Hal9k-dk/bigbro/esp32/main/bigbro.cpp

#include <stdio.h>

#include <esp_app_desc.h>
#include <esp_event.h>
#include <esp_log.h>
#include <esp_wifi.h>
#include <freertos/FreeRTOS.h>
#include <freertos/task.h>
#include <nvs_flash.h>

#include "cardcache.h"
#include "connect.h"
#include "console.h"
#include "controller.h"
#include "defs.h"
#include "display.h"
#include "format.h"
#include "hw.h"
#include "mqtt.h"
#include "nvs.h"
#include "otafwu.h"
#include "reader.h"
#include "sntp.h"

static constexpr const char* TAG = "bigbro";

extern "C"
void app_main()
{
    init_hardware();

    const auto app_desc = esp_app_get_description();
    printf("BigBro v %s\n", app_desc->version);

    mount_spiffs("/spiffs", "font", 10);
    
    TFT_t tft;
    Display display(&tft);
    set_backlight(255);
    
    display.add_progress(format("BigBro v %s", app_desc->version));

    display.add_progress("NVS init");

    init_nvs();

    display.add_progress(get_identifier());

    bool connected = false;
    const auto wifi_creds = get_wifi_creds();
    if (!wifi_creds.empty())
    {
        ESP_ERROR_CHECK(esp_netif_init());
        ESP_ERROR_CHECK(esp_event_loop_create_default());

        display.add_progress("Connect to WiFi");

        int attempts_left = 5;
        while (!connected && attempts_left)
        {
            connected = connect(wifi_creds);
            ESP_LOGI(TAG, "Connected: %d attempts: %d",
                     connected, attempts_left);
            if (!connected)
            {
                disconnect();
                vTaskDelay(10000 / portTICK_PERIOD_MS);
                --attempts_left;
            }
        }
        if (connected)
        {
            ESP_LOGI(TAG, "Connected to WiFi");
            ESP_ERROR_CHECK(esp_wifi_set_ps(WIFI_PS_NONE));

            display.add_progress("SNTP synch");

            initialize_sntp();
            
            Card_cache::instance().set_api_token(get_acs_token());
        }
    }
    
    xTaskCreate(rfid_task, "rfid_task", 4*1024, NULL, 5, NULL);

    printf("\n\nPress a key to enter console\n");
    bool debug = false;
    int keypresses = 0;
    for (int i = 0; i < 20; ++i)
    {
        const int c = getchar();
        if (c != EOF)
        {
            printf("Key: %d\n", c);
            ++keypresses;
            if (keypresses > 3)
            {
                debug = true;
                break;
            }
        }
        vTaskDelay(100/portTICK_PERIOD_MS);
    }

    bool ext1_state = gpio_get_level(PIN_EXT_1);
    bool switch_state = read_switch();
    if (!ext1_state || switch_state)
    {
        display.add_progress("OTA disabled");
        if (!ext1_state)
            printf("OTA firmware update disabled by EXT1\n");
        if (switch_state)
            printf("OTA firmware update disabled by card\n");
    }
    else if (!debug)
    {
        display.add_progress("OTA check");
        if (!check_ota_update(display))
            display.add_progress("FAILED!");
    }
    if (connected)
    {
        xTaskCreate(card_cache_task, "cache_task", 4*1024, NULL, 1, NULL);
        Mqtt::instance().start(get_mqtt_address());
    }
    xTaskCreate(cursense_task, "cursense_task", 2*1024, NULL, 1, NULL);

    if (debug)
        run_console(display);        // never returns

    Mqtt::instance().write_slack(format(":panopticon: BigBro %s", app_desc->version));
    
    esp_log_level_set("esp_wifi", ESP_LOG_ERROR);
    esp_log_level_set("wifi", ESP_LOG_ERROR);

    display.add_progress("Starting");
    Mqtt::instance().log(format("ACS frontend %s (%s)",
                                app_desc->version,
                                get_identifier().c_str()));

    Controller controller(display);
    display.clear();
    controller.run(); // never returns
}

// Local Variables:
// compile-command: "(cd ..; idf.py build)"
// End:
