Hal9k-dk/bigbro/esp32/main/otafwu.cpp

#include "display.h"
#include "http.h"

#include "freertos/FreeRTOS.h"
#include "freertos/task.h"
#include "esp_system.h"
#include "esp_event.h"
#include "esp_log.h"
#include "esp_ota_ops.h"
#include "esp_app_format.h"
#include "esp_http_client.h"
#include "esp_flash_partitions.h"
#include "esp_partition.h"
#include "nvs.h"
#include "nvs_flash.h"
#include "errno.h"

static constexpr const char* TAG = "ota";

static const constexpr int HASH_LEN = 32; // SHA-256 digest length
static const constexpr int BUFFSIZE = 1024;

bool check_ota_update(class Display& display)
{
    // Get SHA256 digest for the partition table
    esp_partition_t partition;
    partition.address   = ESP_PARTITION_TABLE_OFFSET;
    partition.size      = ESP_PARTITION_TABLE_MAX_LEN;
    partition.type      = ESP_PARTITION_TYPE_DATA;
    uint8_t sha_256[HASH_LEN] = { 0 };
    esp_partition_get_sha256(&partition, sha_256);

    // Get SHA256 digest for bootloader
    partition.address   = ESP_BOOTLOADER_OFFSET;
    partition.size      = ESP_PARTITION_TABLE_OFFSET;
    partition.type      = ESP_PARTITION_TYPE_APP;
    esp_partition_get_sha256(&partition, sha_256);

    // Get SHA256 digest for running partition
    esp_partition_get_sha256(esp_ota_get_running_partition(), sha_256);

    const esp_partition_t* running = esp_ota_get_running_partition();
    esp_ota_img_states_t ota_state;
    if (esp_ota_get_state_partition(running, &ota_state) == ESP_OK)
        if (ota_state == ESP_OTA_IMG_PENDING_VERIFY)
        {
            bool diagnostic_is_ok = true;
#if 0
            // later...
            diagnostic_is_ok = diagnostic();
#endif
            if (diagnostic_is_ok)
            {
                ESP_LOGI(TAG, "Diagnostics completed successfully! Continuing execution ...");
                esp_ota_mark_app_valid_cancel_rollback();
            }
            else
            {
                ESP_LOGE(TAG, "Diagnostics failed! Start rollback to the previous version ...");
                esp_ota_mark_app_invalid_rollback_and_reboot();
            }
        }

    const esp_partition_t* configured = esp_ota_get_boot_partition();
    running = esp_ota_get_running_partition();

    if (configured != running)
    {
        ESP_LOGW(TAG, "Configured OTA boot partition at offset 0x%08" PRIx32 ", but running from offset 0x%08" PRIx32,
                 configured->address, running->address);
        ESP_LOGW(TAG, "(This can happen if either the OTA boot data or preferred boot image become corrupted somehow.)");
    }
    ESP_LOGI(TAG, "Running partition type %d subtype %d (offset 0x%08" PRIx32 ")",
             running->type, running->subtype, running->address);

    esp_http_client_config_t config = {
        .host = "acsgateway.hal9k.dk",
        .path = "/firmware/bigbro2",
        .timeout_ms = 3000,
        .event_handler = http_event_handler,
        .transport_type = HTTP_TRANSPORT_OVER_SSL,
        .crt_bundle_attach = esp_crt_bundle_attach,
        .keep_alive_enable = true,
    };

    esp_http_client_handle_t client = esp_http_client_init(&config);
    if (!client)
    {
        ESP_LOGE(TAG, "Failed to initialise HTTP connection");
        return false;
    }
    Http_client_wrapper w(client);
    esp_err_t err = esp_http_client_open(client, 0);
    if (err != ESP_OK)
    {
        ESP_LOGE(TAG, "Failed to open HTTP connection: %s", esp_err_to_name(err));
        return false;
    }
    esp_http_client_fetch_headers(client);
    const int status_code = esp_http_client_get_status_code(client);
    if (status_code != 200)
    {
        ESP_LOGE(TAG, "OTA HTTP error: %d", status_code);
        return false;
    }

    const esp_partition_t* update_partition = esp_ota_get_next_update_partition(NULL);
    assert(update_partition != NULL);
    ESP_LOGI(TAG, "Writing to partition subtype %d at offset 0x%" PRIx32,
             update_partition->subtype, update_partition->address);

    int binary_file_length = 0;
    bool image_header_was_checked = false;
    // update handle : set by esp_ota_begin(), must be freed via esp_ota_end()
    esp_ota_handle_t update_handle = 0;
    while (1)
    {
        char ota_write_data[BUFFSIZE + 1] = { 0 };
        int data_read = esp_http_client_read(client, ota_write_data, BUFFSIZE);
        if (data_read < 0)
        {
            ESP_LOGE(TAG, "Error: SSL data read error");
            return false;
        }
        if (data_read > 0)
        {
            if (!image_header_was_checked)
            {
                if (data_read > sizeof(esp_image_header_t) + sizeof(esp_image_segment_header_t)
                    + sizeof(esp_app_desc_t))
                {
                    // check current version with downloading
                    esp_app_desc_t new_app_info;
                    memcpy(&new_app_info,
                           &ota_write_data[sizeof(esp_image_header_t)
                                           + sizeof(esp_image_segment_header_t)],
                           sizeof(esp_app_desc_t));
                    ESP_LOGI(TAG, "New firmware version: %s", new_app_info.version);

                    esp_app_desc_t running_app_info;
                    if (esp_ota_get_partition_description(running, &running_app_info) == ESP_OK)
                        ESP_LOGI(TAG, "Running firmware version: %s", running_app_info.version);

                    const esp_partition_t* last_invalid_app = esp_ota_get_last_invalid_partition();
                    esp_app_desc_t invalid_app_info;
                    if (esp_ota_get_partition_description(last_invalid_app, &invalid_app_info) == ESP_OK)
                        ESP_LOGI(TAG, "Last invalid firmware version: %s", invalid_app_info.version);

                    // check current version with last invalid partition
                    if (last_invalid_app)
                    {
                        if (memcmp(invalid_app_info.version, new_app_info.version, sizeof(new_app_info.version)) == 0)
                        {
                            ESP_LOGW(TAG, "New version is the same as invalid version.");
                            ESP_LOGW(TAG, "Previously, there was an attempt to launch the firmware with %s version, but it failed.",
                                     invalid_app_info.version);
                            ESP_LOGW(TAG, "The firmware has been rolled back to the previous version.");
                            display.add_progress("Rolled back");
                            return true;
                        }
                    }
                    if (memcmp(new_app_info.version, running_app_info.version, sizeof(new_app_info.version)) == 0)
                    {
                        if (gpio_get_level((gpio_num_t) 0))
                        {
                            ESP_LOGW(TAG, "Current running version is the same as a new. We will not continue the update.");
                            display.add_progress("No new version");
                            return true;
                        }
                        else
                        {
                            ESP_LOGI(TAG, "Forcing update");
                        }
                    }

                    image_header_was_checked = true;

                    err = esp_ota_begin(update_partition, OTA_WITH_SEQUENTIAL_WRITES, &update_handle);
                    if (err != ESP_OK)
                    {
                        ESP_LOGE(TAG, "esp_ota_begin failed (%s)", esp_err_to_name(err));
                        esp_ota_abort(update_handle);
                        return false;
                    }
                    ESP_LOGI(TAG, "esp_ota_begin succeeded");
                    display.add_progress("Downloading");
                }
                else
                {
                    ESP_LOGE(TAG, "received package is not fit len");
                    esp_ota_abort(update_handle);
                    return false;
                }
            }
            err = esp_ota_write(update_handle, (const void*) ota_write_data, data_read);
            if (err != ESP_OK)
            {
                esp_ota_abort(update_handle);
                return false;
            }
            binary_file_length += data_read;
            ESP_LOGD(TAG, "Written image length %d", binary_file_length);
        }
        else if (data_read == 0)
        {
            // As esp_http_client_read never returns negative error code, we rely on
            // `errno` to check for underlying transport connectivity closure if any
            if (errno == ECONNRESET || errno == ENOTCONN)
            {
                ESP_LOGE(TAG, "Connection closed, errno = %d", errno);
                break;
            }
            if (esp_http_client_is_complete_data_received(client))
            {
                ESP_LOGI(TAG, "Connection closed");
                break;
            }
        }
    }
    ESP_LOGI(TAG, "Total Write binary data length: %d", binary_file_length);
    if (!esp_http_client_is_complete_data_received(client))
    {
        ESP_LOGE(TAG, "Error in receiving complete file");
        esp_ota_abort(update_handle);
        return false;
    }

    err = esp_ota_end(update_handle);
    if (err != ESP_OK)
    {
        if (err == ESP_ERR_OTA_VALIDATE_FAILED)
            ESP_LOGE(TAG, "Image validation failed, image is corrupted");
        else 
            ESP_LOGE(TAG, "esp_ota_end failed (%s)!", esp_err_to_name(err));
        return false;
    }

    err = esp_ota_set_boot_partition(update_partition);
    if (err != ESP_OK)
    {
        ESP_LOGE(TAG, "esp_ota_set_boot_partition failed (%s)!", esp_err_to_name(err));
        return false;
    }
    display.add_progress("Rebooting");
    ESP_LOGI(TAG, "Prepare to restart system!");
    esp_restart();
    return true;
}

// Local Variables:
// compile-command: "(cd ..; idf.py build)"
// End:
