Hal9k-dk/bigbro/esp32/components/ili9340/ili9340.h

#ifndef MAIN_ILI9340_H_
#define MAIN_ILI9340_H_

#ifdef __cplusplus
extern "C" {
#endif

#include "driver/spi_master.h"
#include "fontx.h"

#define rgb565(r, g, b) (((r & 0xF8) << 8) | ((g & 0xFC) << 3) | (b >> 3))

#define RED    rgb565(255,   0,   0) // 0xf800
#define GREEN  rgb565(  0, 255,   0) // 0x07e0
#define BLUE   rgb565(  0,   0, 255) // 0x001f
#define BLACK  rgb565(  0,   0,   0) // 0x0000
#define WHITE  rgb565(255, 255, 255) // 0xffff
#define GRAY   rgb565(128, 128, 128) // 0x8410
#define YELLOW rgb565(255, 255,   0) // 0xFFE0
#define CYAN   rgb565(  0, 156, 209) // 0x04FA
#define PURPLE rgb565(128,   0, 128) // 0x8010

typedef enum {DIRECTION0, DIRECTION90, DIRECTION180, DIRECTION270} DIRECTION;

typedef struct {
	uint16_t _model;
	uint16_t _width;
	uint16_t _height;
	uint16_t _offsetx;
	uint16_t _offsety;
	uint16_t _font_direction;
	uint16_t _font_fill;
	uint16_t _font_fill_color;
	uint16_t _font_underline;
	uint16_t _font_underline_color;
	int16_t _dc;
	int16_t _bl;
	int16_t _irq;
	spi_device_handle_t _TFT_Handle;
	spi_device_handle_t _XPT_Handle;
	bool _calibration;
	int16_t _min_xp; // Minimum xp calibration
	int16_t _min_yp; // Minimum yp calibration
	int16_t _max_xp; // Maximum xp calibration
	int16_t _max_yp; // Maximum yp calibration
	int16_t _min_xc; // Minimum x coordinate
	int16_t _min_yc; // Minimum y coordinate
	int16_t _max_xc; // Maximum x coordinate
	int16_t _max_yc; // Maximum y coordinate
} TFT_t;

void spi_master_init(TFT_t * dev, int16_t TFT_MOSI, int16_t TFT_SCLK, int16_t TFT_CS, int16_t GPIO_DC, int16_t GPIO_RESET, int16_t GPIO_BL,
	int16_t XPT_MISO, int16_t XPT_CS, int16_t XPT_IRQ, int16_t XPT_SCLK, int16_t XPT_MOSI);
bool spi_master_write_byte(spi_device_handle_t SPIHandle, const uint8_t* Data, size_t DataLength);
bool spi_master_write_comm_byte(TFT_t * dev, uint8_t cmd);
bool spi_master_write_comm_word(TFT_t * dev, uint16_t cmd);
bool spi_master_write_data_byte(TFT_t * dev, uint8_t data);
bool spi_master_write_data_word(TFT_t * dev, uint16_t data);
bool spi_master_write_addr(TFT_t * dev, uint16_t addr1, uint16_t addr2);
bool spi_master_write_color(TFT_t * dev, uint16_t color, uint16_t size);
bool spi_master_write_colors(TFT_t * dev, uint16_t * colors, uint16_t size);

void delayMS(int ms);
void lcdWriteRegisterWord(TFT_t * dev, uint16_t addr, uint16_t data);
void lcdWriteRegisterByte(TFT_t * dev, uint8_t addr, uint16_t data);
void lcdInit(TFT_t * dev, uint16_t model, int width, int height, int offsetx, int offsety);
void lcdDrawPixel(TFT_t * dev, uint16_t x, uint16_t y, uint16_t color);
void lcdDrawMultiPixels(TFT_t * dev, uint16_t x, uint16_t y, uint16_t size, uint16_t * colors);
void lcdDrawFillRect(TFT_t * dev, uint16_t x1, uint16_t y1, uint16_t x2, uint16_t y2, uint16_t color);
void lcdDrawFillRect2(TFT_t * dev, uint16_t x0, uint16_t y0, uint16_t size, uint16_t color);
void lcdDisplayOff(TFT_t * dev);
void lcdDisplayOn(TFT_t * dev);
void lcdInversionOff(TFT_t * dev);
void lcdInversionOn(TFT_t * dev);
void lcdBGRFilter(TFT_t * dev);
void lcdFillScreen(TFT_t * dev, uint16_t color);
void lcdDrawLine(TFT_t * dev, uint16_t x1, uint16_t y1, uint16_t x2, uint16_t y2, uint16_t color);
void lcdDrawRect(TFT_t * dev, uint16_t x1, uint16_t y1, uint16_t x2, uint16_t y2, uint16_t color);
void lcdDrawRect2(TFT_t * dev, uint16_t x0, uint16_t y0, uint16_t size, uint16_t color);
void lcdDrawRectAngle(TFT_t * dev, uint16_t xc, uint16_t yc, uint16_t w, uint16_t h, uint16_t angle, uint16_t color);
void lcdDrawTriangle(TFT_t * dev, uint16_t xc, uint16_t yc, uint16_t w, uint16_t h, uint16_t angle, uint16_t color);
void lcdDrawRegularPolygon(TFT_t * dev, uint16_t xc, uint16_t yc, uint16_t n, uint16_t r, uint16_t angle, uint16_t color);
void lcdDrawCircle(TFT_t * dev, uint16_t x0, uint16_t y0, uint16_t r, uint16_t color);
void lcdDrawFillCircle(TFT_t * dev, uint16_t x0, uint16_t y0, uint16_t r, uint16_t color);
void lcdDrawRoundRect(TFT_t * dev, uint16_t x1, uint16_t y1, uint16_t x2, uint16_t y2, uint16_t r, uint16_t color);
void lcdDrawArrow(TFT_t * dev, uint16_t x0, uint16_t y0, uint16_t x1, uint16_t y1, uint16_t w, uint16_t color);
void lcdDrawFillArrow(TFT_t * dev, uint16_t x0, uint16_t y0, uint16_t x1, uint16_t y1, uint16_t w, uint16_t color);
int lcdDrawChar(TFT_t * dev, FontxFile *fx, uint16_t x, uint16_t y, uint8_t ascii, uint16_t color);
int lcdDrawString(TFT_t * dev, FontxFile *fx, uint16_t x, uint16_t y, const uint8_t * ascii, uint16_t color);
int lcdDrawCode(TFT_t * dev, FontxFile *fx, uint16_t x,uint16_t y,uint8_t code,uint16_t color);
//int lcdDrawSJISChar(TFT_t * dev, FontxFile *fx, uint16_t x, uint16_t y, uint16_t sjis, uint16_t color);
//int lcdDrawUTF8Char(TFT_t * dev, FontxFile *fx, uint16_t x, uint16_t y, uint8_t *utf8, uint16_t color);
//int lcdDrawUTF8String(TFT_t * dev, FontxFile *fx, uint16_t x, uint16_t y, unsigned char *utfs, uint16_t color);
void lcdSetFontDirection(TFT_t * dev, uint16_t);
void lcdSetFontFill(TFT_t * dev, uint16_t color);
void lcdUnsetFontFill(TFT_t * dev);
void lcdSetFontUnderLine(TFT_t * dev, uint16_t color);
void lcdUnsetFontUnderLine(TFT_t * dev);
void lcdBacklightOff(TFT_t * dev);
void lcdBacklightOn(TFT_t * dev);
void lcdSetScrollArea(TFT_t * dev, uint16_t tfa, uint16_t vsa, uint16_t bfa);
void lcdResetScrollArea(TFT_t * dev, uint16_t vsa);
void lcdScroll(TFT_t * dev, uint16_t vsp);
int xptGetit(TFT_t * dev, int cmd);
bool touch_getxy(TFT_t *dev, int *xp, int *yp);

#ifdef __cplusplus
}
#endif

#endif /* MAIN_ILI9340_H_ */
