Hal9k-dk/bigbro/esp32/main/hw.h

#pragma once

#include "util.h"

void init_hardware();

bool read_switch();

void set_relay(bool on);

void set_backlight(int backlight);

void fade_backlight(int backlight, int ms);
void fade_backlight(int backlight, util::duration dur);

bool read_current_sensor();

extern "C" void cursense_task(void*);

// Local Variables:
// compile-command: "(cd ..; idf.py build)"
// End:
