Hal9k-dk/bigbro/esp32/main/sntp.cpp

#include "defs.h"

#include "freertos/FreeRTOS.h"
#include "freertos/task.h"
#include "esp_log.h"
#include "esp_sntp.h"

static constexpr const char* TAG = "sntp";

void initialize_sntp()
{
    ESP_LOGI(TAG, "Initializing SNTP");
    esp_sntp_setoperatingmode(SNTP_OPMODE_POLL);
    esp_sntp_setservername(0, "pool.ntp.org");
#ifdef CONFIG_SNTP_TIME_SYNC_METHOD_SMOOTH
    sntp_set_sync_mode(SNTP_SYNC_MODE_SMOOTH);
#endif
    esp_sntp_init();

    // wait for time to be set
    int retry = 0;
    const int retry_count = 10;
    while (sntp_get_sync_status() == SNTP_SYNC_STATUS_RESET && ++retry < retry_count)
    {
        ESP_LOGI(TAG, "Waiting for system time to be set... (%d/%d)", retry, retry_count);
        vTaskDelay(2000 / portTICK_PERIOD_MS);
    }
}

// Local Variables:
// compile-command: "cd .. && idf.py build"
// End:
