Hal9k-dk/bigbro/firmware/src/acsrestclient.cpp

#include "acsrestclient.h"

AcsRestClient::AcsRestClient(const char* p):
    path(p)
{
}

int AcsRestClient::post(const JsonObject& obj)
{
    String s;
    obj.printTo(s);
    // Work around RestClient bug
    s = String("\r\n") + s;
    RestClient client(SERVER, USE_SSL ? 443 : 80, USE_SSL);
    client.setContentType("application/json");
    String url("/api/v1/");
    url += path;
    return client.post(url.c_str(), s.c_str(), &response);
}

String AcsRestClient::get_response() const
{
    return response;
}
