Hal9k-dk/bigbro/esp32/main/util.cpp

#include "util.h"

#include <stdio.h>

#include "cJSON.h"

void fatal_error(const char* msg)
{
    printf("FATAL: %s\n", msg);
    // TODO
    
}

namespace util
{

std::string strip_np(const std::string& s)
{
    std::string result;
    for (auto c : s)
        if (isprint(c))
            result += c;
    return result;
}

time_t make_timestamp(char* stamp, bool with_tz)
{
    time_t current = 0;
    time(&current);
    make_timestamp(current, stamp, with_tz);
    return current;
}

void make_timestamp(time_t t, char* stamp, bool with_tz)
{
    struct tm timeinfo;
    gmtime_r(&t, &timeinfo);
    strftime(stamp, TIMESTAMP_SIZE,
             with_tz ? "%Y-%m-%dT%H:%M:%S+00:00" : "%Y-%m-%dT%H:%M:%S",
             &timeinfo);
}

} // end namespace

cJSON_wrapper::cJSON_wrapper(cJSON*& json)
    : json(json)
{
}

cJSON_wrapper::~cJSON_wrapper()
{
    if (json)
        cJSON_Delete(json);
    json = nullptr;
}

cJSON_Print_wrapper::cJSON_Print_wrapper(char*& json)
    : json(json)
{
}

cJSON_Print_wrapper::~cJSON_Print_wrapper()
{
    if (json)
        free(json);
    json = nullptr;
}

// Local Variables:
// compile-command: "cd .. && idf.py build"
// End:
